SimonHawk/zmk-config-HawkV02/ergogen/HawkV0_output_prod/outlines/switches.dxf

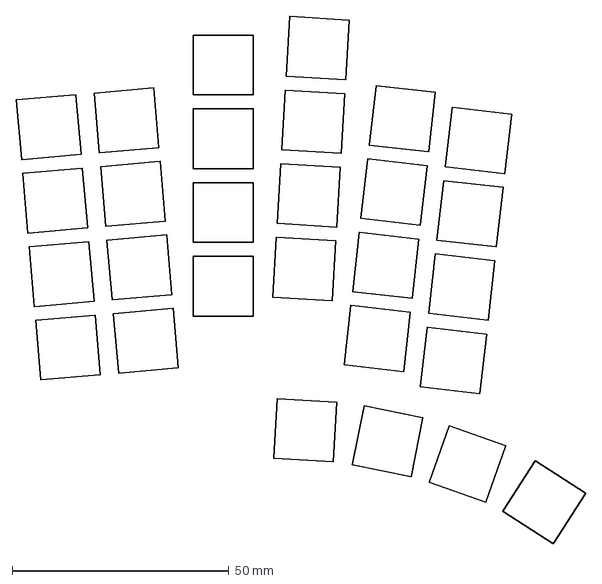
[picture p15: CAD file, 2025-06-04]
ergogen/HawkV0_output_prod/outlines/switches.dxf
131.2 x 121.5 mm
