SimonHawk/zmk-config-HawkV02/ergogen/HawkV0_output_prod/outlines/cutout_circle_thumb.dxf

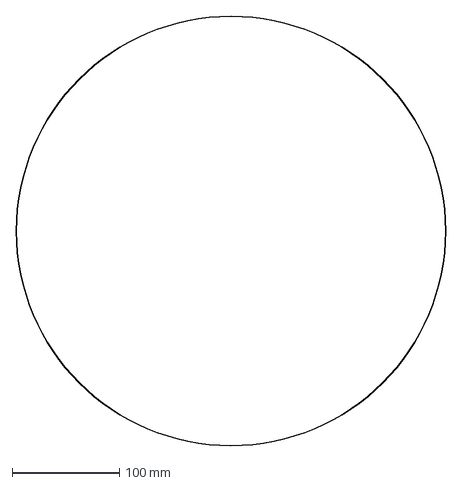
[picture p16: CAD file, 2025-06-04]
ergogen/HawkV0_output_prod/outlines/cutout_circle_thumb.dxf
400.0 x 400.0 mm
