SimonHawk/zmk-config-HawkV02/ergogen/HawkV0_output_prod/outlines/plate_test.dxf

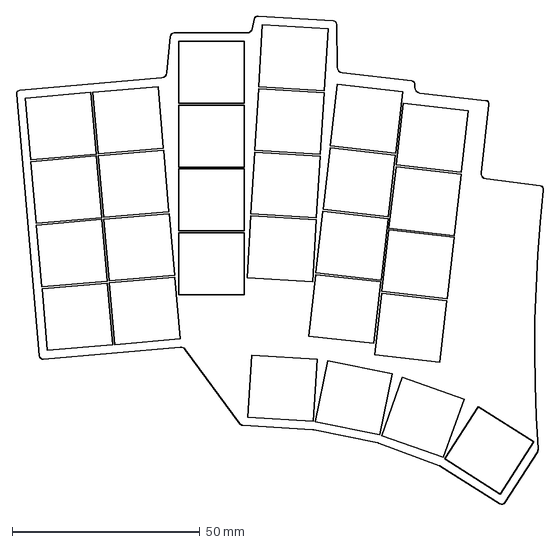
[picture p17: CAD file, 2025-06-04]
ergogen/HawkV0_output_prod/outlines/plate_test.dxf
140.6 x 130.3 mm
